kowalej/AnemIO/src/raspi-base/raspi-config-files/config.txt

hdmi_force_hotplug=1
enable_uart=0

# camera settings, see http://elinux.org/RPiconfig#Camera
start_x=0
disable_camera_led=1
gpu_mem=16


# Enable audio (added by raspberrypi-sys-mods)
dtparam=audio=on
dtparam=spi=on
