kowalej/AnemIO/src/arduino-station/Pair.h

#ifndef PAIR_H
#define PAIR_H JUN_2014

/* Lightweight implementation of STL Pair<> */

template<class M, class N>
struct Pair {
	M val_1;
	N val_2;

	Pair() :val_1(NULL), val_2(NULL) {}
	
	Pair(int n) : val_1(NULL), val_2(NULL) {}

	Pair(M v1, N v2)
		:val_1(v1), val_2(v2) {}

	//use default values for copy construction and assignment

	M first() { return val_1; }
	const M first() const { return val_1; }

	N second() { return val_2; }
	const N second() const { return val_2; }
};

#endif
