kowalej/AnemIO/src/arduino-station/PressureProvider.cpp

#include "PressureProvider.h"

PressureProvider::PressureProvider() : bmx280(BMP280_IC2_ADDRESS) {}

bool PressureProvider::setup() {
	// Check the interface, and read the sensor ID (to differentiate between BMP280 and BME280).
	if (!bmx280.begin())
	{
		debugE("Setup failed, cannot find valid BMP or BME 280 device. Check wiring and your BMx280 Interface / I2C Address.");
		_isOnline = false;
		return _isOnline;
	}

	if (bmx280.isBME280()) {
		debugI("Sensor found: BME280.");
	}
	else {
		debugI("Sensor found: BMP280.");
	}

	// Reset sensor to default parameters.
	bmx280.resetToDefaults();
	
	// By default sensing is disabled and must be enabled by setting a non-zero oversampling setting.
	// Set an oversampling setting for pressure and temperature measurements. 
	bmx280.writeOversamplingPressure(BMx280MI::OSRS_P_x04); // x04 should provide good resolution.
	bmx280.writeOversamplingTemperature(BMx280MI::OSRS_T_x01); // x01 is good enough for temperature resolution.
	bmx280.writeFilterSetting(BMx280MI::FILTER_OFF); // Do not filter, since this is for weather measurement, and pressure fluctuations are useful.

	// If sensor is a BME280, set an oversampling setting for humidity measurements.
	if (bmx280.isBME280())
		bmx280.writeOversamplingHumidity(BMx280MI::OSRS_P_x04);

	_isOnline = true;
	return _isOnline;
}

void PressureProvider::measure() {
	bmx280.writePowerMode(BMx280MI::power_mode_t::BMx280_MODE_FORCED); // Must write power mode to start a forced measurement.

	// Start a measurement.
	if (!bmx280.measure())
	{
		return;
	}

	// Wait for the measurement to finish.
	do
	{
		delay(1);
	} while (!bmx280.hasValue());

	_pressureRead = false;
	_temperatureRead = false;
	_altitudeRead = false;
}

float PressureProvider::getPressure() {
	if (_pressureRead) {
		measure();
	}
	_pressureRead = true;
	_lastPressure = bmx280.getPressure();
	return _lastPressure;
}

float PressureProvider::getTemperature() {
	if (_temperatureRead) {
		measure();
	}
	_temperatureRead = true;
	return bmx280.getTemperature();
}

float PressureProvider::getAltitude() {
	if (_altitudeRead) {
		measure();
	}
	_altitudeRead = true;
	
	float altitude;
	float pressure = _lastPressure != NAN ? _lastPressure : getPressure();
	float pressurehPa = pressure/100; // Convert to hPA (aka millibar).

	// Use crazy formula to get altitude in meters. See https://en.wikipedia.org/wiki/Pressure_altitude.
	altitude = 44307.69396 * (1.0 - pow(pressurehPa / 1013.25, 0.190284));

	return altitude;
}
